republicofmakers/HW-KICAD-MCU-STM32-External-ADC-DAC/Documents/Pictures/Picture-JLCPCB.png

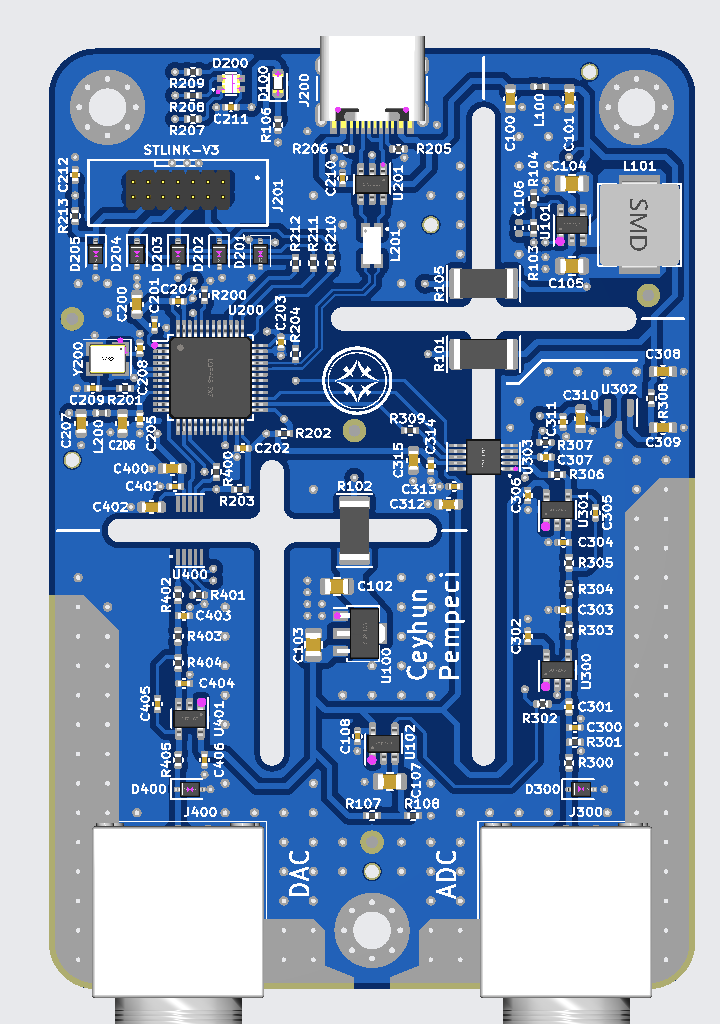
Documents/Pictures/Picture-JLCPCB.png
