republicofmakers/HW-KICAD-MCU-STM32-External-ADC-DAC/Documents/LTSpice_simulations/3rd_order_bw_filter/3rd_order_bw_filter.asc

C301: cap; 100nF
C303: cap; 1nF
C304: cap; 150pF
C305: cap; 1nF
C307: cap; 150p
R302: res; 2.2MegO
R303: res; 6.8kO
R304: res; 22kO
R305: res; 12kO
R306: res; 1kO
R307: res; 1kO
U300: AD820
U301: AD820
V1: voltage; 0; AC 1 0
V2: voltage; 3.3V
V3: voltage; 1.65V
Named nets: 0, vcc, vin, vcom, filter_vout, filter_vin, follower_vin, filter_fb, vout_plus, vout_minus
3rd order Sallen-Key Butterworth Filter, for ADC and DAC anti-aliasing
Low-pass topology, Fc = 25 kHz
;.op
.ac dec 100 0.1 100MEG
